Xeraster/fpga_videocard_16bit/fpga_videocard.pcf

set_io pixelClock 52
#set_io clock1024 55
set_io HOST_RESET 1
set_io HSYNC 16
set_io VSYNC 15

#vga output bits
set_io Red[0] 21    #VD11
set_io Red[1] 128    #use this pin instead because of a routing mistake
set_io Red[2] 19
set_io Red[3] 18
set_io Red[4] 17    #VD15

set_io Green[0] 28    #VD05
set_io Green[1] 26
set_io Green[2] 25
set_io Green[3] 24
set_io Green[4] 23
set_io Green[5] 22    #VD10

set_io Blue[0] 34    #VD00
set_io Blue[1] 33
set_io Blue[2] 32
set_io Blue[3] 31
set_io Blue[4] 29    #VD04

#vram address bus
set_io AV[0] 107
set_io AV[1] 106
set_io AV[2] 105
set_io AV[3] 104
set_io AV[4] 102
set_io AV[5] 101
set_io AV[6] 99
set_io AV[7] 98
set_io AV[8] 97
set_io AV[9] 96
set_io AV[10] 95
set_io AV[11] 91
set_io AV[12] 90
set_io AV[13] 88
set_io AV[14] 87
set_io AV[15] 85
set_io AV[16] 84
set_io AV[17] 83
set_io AV[18] 82
set_io AV[19] 81

#16 bit vram data bus
set_io DS[0] 144
set_io DS[1] 143
set_io DS[2] 142
set_io DS[3] 141
set_io DS[4] 139
set_io DS[5] 138
set_io DS[6] 137
set_io DS[7] 136
set_io DS[8] 135
set_io DS[9] 134
set_io DS[10] 130
set_io DS[11] 125
set_io DS[12] 124
set_io DS[13] 122
set_io DS[14] 121
set_io DS[15] 120

#sram chip control signals
set_io read_cmd 41
set_io write_cmd 39
set_io VRAM_low_en 37
set_io VRAM_high_en 38

set_io VGASCK 63
set_io VGAMOSI 60
set_io VGAMISO 56
set_io VGACS0 49

#just test ports, nothing special
set_io DEBUG0 93    #u2
set_io DEBUG1 110   #u1
set_io MCLK0 4
set_io MCLK1 7

#isa related stuff
set_io SBHE 62
set_io BALE 61
set_io IOCS16 74
set_io MEMCS16 73
set_io IOERR 44
set_io IO_RDY 117
set_io NOWS 45
set_io ADS_OE 42
set_io ADS_LATCH 43
set_io MEMR 119
set_io MEMW 118
set_io SMEMR 76
set_io SMEMW 75
set_io IOR 79
set_io IOW 78
set_io ISACLK 94

set_io FPGA_WR 116
set_io TE0 115
set_io TE1 114
set_io TE2 113
set_io TE3 112
set_io FASTCLK 55
set_io isa_ctrl_out_en 80
