Xeraster/fpga_videocard_16bit/new_fifo/sync_r2w.v

//
// Read pointer to write clock synchronizer
//
module sync_r2w
#(
  parameter ADDRSIZE = 8
)
(
  input   wclk, wrst_n,
  input   [ADDRSIZE:0] rptr,
  output reg  [ADDRSIZE:0] wq2_rptr//readpointer with write side
);

  reg [ADDRSIZE:0] wq1_rptr;

  always@(posedge wclk or negedge wrst_n)
    if (!wrst_n) {wq2_rptr,wq1_rptr} <= 0;
    else {wq2_rptr,wq1_rptr} <= {wq1_rptr,rptr};

endmodule
