Xeraster/fpga_videocard_16bit/new_fifo/syncw2r.v

module sync_w2r
#(
  parameter ADDRSIZE = 8
)
(
  input   rclk, rrst_n,
  input   [ADDRSIZE:0] wptr,
  output reg [ADDRSIZE:0] rq2_wptr
);

  reg [ADDRSIZE:0] rq1_wptr;

  always@(posedge rclk or negedge rrst_n)
    if (!rrst_n)
      {rq2_wptr,rq1_wptr} <= 0;
    else
      {rq2_wptr,rq1_wptr} <= {rq1_wptr,wptr};

endmodule
